DLFW/FogDrive/source/mcus/atmega328p.h

/*
    FogDrive (https://github.com/FogDrive/FogDrive)
    Copyright (C) 2016  Daniel Llin Ferrero

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
    You should have received a copy of the GNU General Public License
    along with this program.  If not, see <http://www.gnu.org/licenses/>.
*/

#ifndef ATMEGA328P_H
#define ATMEGA328P_H

#include <avr/io.h>

/**************************************************
 * UI input
 *************************************************/
#define HWMAP_UI_SWITCH_DDR      DDRB
#define HWMAP_UI_SWITCH_PORT     PORTB
#define HWMAP_UI_SWITCH_PIN      PINB
#define HWMAP_UI_SWITCH_0_IX     3

/**************************************************
 * UI output
 *************************************************/
#define HWMAP_UI_OUTPIN_DDR     DDRB
#define HWMAP_UI_OUTPIN_PORT    PORTB
#define HWMAP_UI_OUTPIN_0_IX    2

/**************************************************
 * UI timer for event timing
 *************************************************/
#define HWMAP_UI_TIMER_ISR     TIMER2_OVF_vect
#define HWMAP_UI_TIMER_CMD_REINIT_FOR_10ms TCNT2 = (256-(F_CPU / 256 * 10e-3 + 0.5));
// Function that initializes the UI timers and PWMs
void ui_timer_init_10ms_overflow(void);

/**************************************************
 * UI timer for LED PWM
 *************************************************/
#define MCU_UI_PWM_A_CR OCR0A
void mcu_init_ui_double_compare_timer_for_fast_pwm_1ms(void);

/**************************************************
 * UART
 *************************************************/
#define UART_ENABLED
// Baud rate for the UART, should be externalized somehow later on
#define BAUD 4800UL
// The UART's char buffer register (delivers in received character inside the ISR and takes a charater to write out)
#define CTRLMAP_UART_CHARBUFFER     UDR0
// Command that waits until the charbuffer is empty and can be used to send a single character
#define MCUMAP_UART_CMD_AWAIT_EMPTY_CHARBUFFER  while ( !( UCSR0A & (1<<UDRE0)) );
// Function that inititializes the UART with 8 data and one stop bit.
void uart_init_8_plus_1(void);

/**************************************************
 * Hardware fire pin
 *************************************************/
// Data register used to control the fire MOSFET
#define HWMAP_HW_FIRE_DDR        DDRB
// Corresponding port
#define HWMAP_HW_FIRE_PORT       PORTB
// Index of the pin used to control the fire MOSFET
#define HWMAP_HW_FIRE_BIT_IX     0

/**************************************************
 * Hardware ADC
 *************************************************/
void mcu__enabled_one_adc_with_vcc_reference_and_vgb_input(void);
#define MCU__START_SINGLE_ADC_CONVERSION ADCSRA |= (1<<ADSC)
#define MCU__SINGLE_ADC_CONVERSION_IS_DONE ! (ADCSRA & (1<<ADSC))

/**************************************************
 * Power Down
 *************************************************/
void mcu_power_down_till_pin_change(void);

#endif // ATMEGA328P_H
