DLFW/FogDrive/source/mcus/atmega328p.c

/*
    FogDrive (https://github.com/FogDrive/FogDrive)
    Copyright (C) 2016  Daniel Llin Ferrero

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
    You should have received a copy of the GNU General Public License
    along with this program.  If not, see <http://www.gnu.org/licenses/>.
*/

#include "atmega328p.h"
#include <avr/interrupt.h>
#include <avr/sleep.h>


// Baud rate related calculation
#define UBRR_VAL ((F_CPU+BAUD*8)/(BAUD*16)-1)   // clever runden
#define BAUD_REAL (F_CPU/(16*(UBRR_VAL+1)))     // Reale Baudrate
#define BAUD_ERROR ((BAUD_REAL*1000)/BAUD)      // Fehler in Promille, 1000 = kein Fehler.

#if ((BAUD_ERROR<990) || (BAUD_ERROR>1010))
#error Systematic error of baud rate to high (> 1%). Aborting.
#endif

void uart_init_8_plus_1(void) {
    UBRR0H = UBRR_VAL >> 8;
    UBRR0L = UBRR_VAL & 0xFF;
    UCSR0B |= (1<<TXEN0) | (1<<RXEN0) | (1<<RXCIE0);  // enable send, enable receive, enable receive interrupt
    UCSR0C = (1<<UCSZ01)| (1<<UCSZ00)|(1<<UCPOL0);    // asynch 8 bit + 1 stop bit
}

void ui_timer_init_10ms_overflow(void) {
    TCCR2B = (1<<CS22)|(1<<CS21);  // prescaler 256
    TIMSK2 = (1<<TOIE2);
    HWMAP_UI_TIMER_CMD_REINIT_FOR_10ms;
}

void mcu_init_ui_double_compare_timer_for_fast_pwm_1ms(void) {
    //TODO: it's only 1ms with 1MHz frequency: refactor name or function
    DDRD |= (1<<6);                                   // Set the pin of PWM channel A as output
    TCCR0A = (1<<WGM01) | (1<<WGM00) | (1<<COM0A1) | (1<<COM0A0);   // Fast PWM, single slope, count from 0 to 255 (not only till compare), inverting
    TCCR0B = (1<<CS00);                               // Internal clock, no prescaling
}

void mcu__enabled_one_adc_with_vcc_reference_and_vgb_input(void) {
    ADMUX |= (1<<REFS0);                         //voltage reference selction: AV_CC
    ADMUX |= (1<<MUX3) | (1<<MUX2) | (1<<MUX1);  //input voltage selection: 1.1V (V_BG)
    ADCSRA |= (1<<ADEN);                         //activate ADC
}

void mcu_power_down_till_pin_change(void) {
    PCICR |= (1 << PCIE0);                      //enable pin change iterrupt on PCINT[7..0] which includes the button
    PCMSK0 |= (1 << PCINT3);                    // and activate the PCINT for the button pin
    set_sleep_mode(SLEEP_MODE_PWR_DOWN);        // set sleep mode (power down, deepest sleep)...
    sleep_mode();                               // ...and enter it
    PCICR &= ~(1 << PCIE0);                     // we're waking up! disable pin change iterrupt on PCINT[7..0]
}

ISR(PCINT0_vect) {
    // Nothing to do in this interrupt routine.
    // It must just be defined since we need that interrupt to awake from "power down" sleep mode.
}
