DLFW/FogDrive/source/mira/deviface.c

/*
    FogDrive (https://github.com/FogDrive/FogDrive)
    Copyright (C) 2016  Daniel Llin Ferrero

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
    You should have received a copy of the GNU General Public License
    along with this program.  If not, see <http://www.gnu.org/licenses/>.
*/

#include <avr/io.h>
#include <avr/interrupt.h>
#include <string.h>
#include "queue.h"
#include "deviface.h"
#include MCUHEADER

volatile uint8_t uart_str_complete = 0;
volatile uint8_t uart_str_count = 0;
volatile char uart_string[UART_MAXSTRLEN + 1] = "";


#ifdef UART_ENABLED

void deviface_init(void) {
    uart_init_8_plus_1();
}

void deviface_putchar( unsigned char data ) {
#ifdef UART_ENABLED
    // Wait for empty transmit buffer (mcu specific macro)
    MCUMAP_UART_CMD_AWAIT_EMPTY_CHARBUFFER;
    // Put data into buffer (mcu specific macro), sends the data
    CTRLMAP_UART_CHARBUFFER = data;
#endif
}

void deviface_putstring (char* s) {
    while (*s) {
        deviface_putchar(*s);
        s++;
    }
}

void deviface_putlineend(void) {
    deviface_putstring("\r\n");
}

void deviface_putline (char* s) {
    deviface_putstring(s);
    deviface_putlineend();
}

void deviface_put_uint8(uint8_t v) {
    char value_s[4];
    utoa(v,value_s,10);
    deviface_putstring(value_s);
}

void deviface_put_int8(int8_t v) {
    char value_s[4];
    itoa(v,value_s,10);
    deviface_putstring(value_s);
}

void deviface_put_uint16(uint16_t v) {
    char value_s[6];
    utoa(v,value_s,10);
    deviface_putstring(value_s);
}

void deviface_put_float(float v, int8_t width, uint8_t prec) {
    char value_s[20];
    dtostrf(v, width, prec,value_s);
    deviface_putstring(value_s);
}

ISR(USART_RX_vect) {
#ifdef UART_ENABLED
  unsigned char nextChar;
  nextChar = CTRLMAP_UART_CHARBUFFER;
  if( uart_str_complete == 0 ) {
    if( nextChar != '\n' &&
        nextChar != '\r' &&
        uart_str_count < UART_MAXSTRLEN
    ) {
        uart_string[uart_str_count] = nextChar;
        uart_str_count++;
        deviface_putchar(nextChar);            // echo the character
    } else {
        uart_string[uart_str_count] = '\0';
        uart_str_count = 0;
        uart_str_complete = 1;
        deviface_putchar('\r');
        deviface_putchar('\n');
    }
  }
#endif
}

#endif
