DLFW/FogDrive/source/mira/ui.c

/*
    FogDrive (https://github.com/FogDrive/FogDrive)
    Copyright (C) 2016  Daniel Llin Ferrero

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
    You should have received a copy of the GNU General Public License
    along with this program.  If not, see <http://www.gnu.org/licenses/>.
*/

#include <avr/io.h>
#include <avr/interrupt.h>
#include <avr/delay.h>
#include "ui.h"
#include "logic.h"
#include "led.h"
#include "button.h"
#include MCUHEADER
#ifdef UART_ENABLED
    #include "deviface.h"
#endif

// Bit mask for switch 0
#define CTRLMAP_SWITCH_0_MASK   (1<<HWMAP_UI_SWITCH_0_IX)
// Bit mask for all used switches
#define ALL_SWITCHES            (1<<HWMAP_UI_SWITCH_0_IX)

// Bit mask for out pin 0 (LED)
#define OUTPIN_0_MASK           (1<<HWMAP_UI_OUTPIN_0_IX)
// Bit mask for all used out pins
#define OUTPIN_ALL_MASK         (1<<HWMAP_UI_OUTPIN_0_IX)

// Low Level Event codes (for the low_level_event_queue)
#define LLE_SWITCH_PRESSED 1    // a switch was pressed, switch index in 2nd queue element
#define LLE_SWITCH_RELEASED 2   // a switch was released, switch index in 2nd queue element
#define LLE_50MS_PULSE 3        // 50 ms pulse, this event is put in the queue each 50 ms

// User interface input queue (which is an external, see @ui.h#Queue ui_input_queue) and its element array
Queue ui_event_queue;
QueueElement ui_event_queue_elements[4];

/**
 * Queue that transports low level control events to the ui state machines.
 * It's used locally in this module only.
 * Its elements carry a "Low Level Event" (LLE_*) in byte a. In case the event refers to a switch,
 * the switch index is in byte b.
 */
static Queue low_level_event_queue;
/**
 * Queue array for #ui_input_queue.
 */
static QueueElement low_level_event_queue_array[3];

static LED led;

static Button button;

static uint8_t ui_local_bools = 0;
#define LB_PRINT_LED_INFO       1
#define LB_FIRE_IS_ON           2
#define LB_LOW_VOLTAGE_DETECTED 4
#define LB_VERY_LOW_VOLTAGE_DETECTED 8
#define LB_SWITCH_OFF_FORCED    16

/**
 * @brief Blends the LED from a value "from" to a value "to".
 */
void led_blend(void) {
    led_program_reset(&led);
    led_program_add_brightness(&led, 0);
    led_program_add_linear_dim(&led, 99, 50);
    led_program_add_brightness(&led, 0);
    led_start_program(&led);
}

uint8_t ui_init(void) {
    // init queues
    queue_initialize(&ui_event_queue, 4, ui_event_queue_elements);
    queue_initialize(&low_level_event_queue, 3, low_level_event_queue_array);

    // init switch pins
    HWMAP_UI_SWITCH_DDR &= ~ALL_SWITCHES;                // configure all input pins as input by setting the related direction bits to 0
    HWMAP_UI_SWITCH_PORT |= ALL_SWITCHES;                // turn on the pull up resistors of all input pins

    // init output pin
    HWMAP_UI_OUTPIN_DDR |= OUTPIN_ALL_MASK;             // configure output pins as output in the related data direction register
    HWMAP_UI_OUTPIN_PORT &= ~OUTPIN_ALL_MASK;           // initialize all output pins (set them off)

    // init the ui timer
    ui_timer_init_10ms_overflow();

    // init LED PWM
    mcu_init_ui_double_compare_timer_for_fast_pwm_1ms();
    led_init_led(&led, &MCU_UI_PWM_A_CR);

    // init button logic
    button_init(&button);

    led_blend();

    return 0;
}

/**
  * ISR for timer zero.
  * Configured to be called every 10ms.
  */
ISR( HWMAP_UI_TIMER_ISR ) {
    // initialize the timer again to get the wanted trigger frequency for this ISR
    HWMAP_UI_TIMER_CMD_REINIT_FOR_10ms;

    // debouncing counter bytes
    static uint8_t ct0 = 0xFF, ct1 = 0xFF;
    // latest debounced switch state (each bit represents one switch (bit) from the input register (PIN))
    static uint8_t switch_states = 0;
    // latest changed status (1 = changed, 0 = unchanged, each bit represents one switch (bit) from the input register (PIN))
    static uint8_t changed_switches = 0;
    // counter that just counts to five times and is resetted then to identify each 5th cycle of the 10ms branch
    static uint8_t _50ms_counter = 0;
    // stores the difference of the main cycle counter between each call and the former of this ISR
    static uint8_t last_main_cycle_counter = 0;

    // here we go...
    // debouncing:
    // basic debouncing strategy based on http://www.mikrocontroller.net/articles/Entprellung#Timer-Verfahren_.28nach_Peter_Dannegger.29
    //
    // set those bits in i to 1 which represents a switch whose actual state is different from the latest unbounced state (key_state)
    uint8_t i = switch_states ^ ~HWMAP_UI_SWITCH_PIN;
    // ct0 and ct1 bytes: count the number of subsequent differences between actual and last debounced state or set back it back to 0 if it's equal.
    ct0 = ~( ct0 & i );
    ct1 = ct0 ^ (ct1 & i);
    // for each switch that had 4 times an actual state different from the last debounced state, set the corresponding bit in i to 1
    i &= ct0 & ct1;
    // set the most current _debounced_ state of all switches
    switch_states ^= i;
    // create a bitmask of all _relevant_ switches that have changed
    changed_switches = i & ALL_SWITCHES;

    // check for concrete switch changes:
    // check for switch 0
    if (CTRLMAP_SWITCH_0_MASK & changed_switches) {
        QueueElement* e = queue_get_write_element(&low_level_event_queue);
        if (CTRLMAP_SWITCH_0_MASK & switch_states) {
            e->bytes.a = LLE_SWITCH_PRESSED;
        } else {
            e->bytes.a = LLE_SWITCH_RELEASED;
        }
        e->bytes.b = HWMAP_UI_SWITCH_0_IX;
    }

    if (++_50ms_counter == 5) {
        _50ms_counter = 0;
        QueueElement* e = queue_get_write_element(&low_level_event_queue);
        e->bytes.a = LLE_50MS_PULSE;
    }

    led_step(&led);
}

void _print_led_commands(LED* led) {
#ifdef UART_ENABLED
    uint8_t n = 0;
    for (n = 0; n < _LED_MAX_COMMAND_COUNT; n++) {
        deviface_putstring("  ");
        deviface_put_uint8(led->_commands[n].cmd);
        deviface_putstring(" ");
        deviface_put_uint8(led->_commands[n].generic.a);
        deviface_putstring(" ");
        deviface_put_uint8(led->_commands[n].generic.b);
        deviface_putstring(" ");
        deviface_put_uint8(led->_commands[n].generic.c);
        deviface_putlineend();
    }
#endif
}

void _callback_for_shutdown(LED *led) {
    // we are switched on (awake) and switch off now (go to sleep)
    QueueElement* e = queue_get_write_element(&ui_event_queue);
    e->bytes.a = UI__SWITCH_OFF;
}

void ui_input_step(void) {

    // Check for events from the timer ISR and react
    QueueElement* low_level_event_e = queue_get_read_element(&low_level_event_queue);
    if (low_level_event_e != 0) {
        if (low_level_event_e->bytes.a == LLE_SWITCH_PRESSED) {
            button_pressed(&button);
        }
        else if (low_level_event_e->bytes.a == LLE_SWITCH_RELEASED) {
            button_released(&button);
        }
        else if (low_level_event_e->bytes.a == LLE_50MS_PULSE) {
            QueueElement* e = queue_get_write_element(&ui_event_queue);
            e->bytes.a = UI__50MS_PULSE;
            button_step(&button);
        }
    }

    // Check for events from the button and react
    if (global_state == GS_AWAKENING) {
        QueueElement* button_event = queue_get_read_element(&(button.button_event_queue));
        if (button_event != 0) {
            if (button_event->bytes.a == BUTTON_EVENT_CLICK & button_event->bytes.b == 3) {
                QueueElement* e = queue_get_write_element(&ui_event_queue);
                e->bytes.a = UI__SWITCH_ON;
            } else {
                QueueElement* e = queue_get_write_element(&ui_event_queue);
                e->bytes.a = UI__ABORT_AWAKENING;
            }
        }

    } else {
        QueueElement* button_event = queue_get_read_element(&(button.button_event_queue));
        if (button_event != 0) {
            switch (button_event->bytes.a) {
                case BUTTON_EVENT_PRESSED: {
                    // button pressed: fire!
                    QueueElement* e = queue_get_write_element(&ui_event_queue);
                    e->bytes.a = UI__FIRE_BUTTON_PRESSED;
                    break;
                }
                case BUTTON_EVENT_RELEASED_TIMEOUT: {
                    led_blend();
                    break;
                }
                case BUTTON_EVENT_TIMEOUT:
                case BUTTON_EVENT_RELEASED: {
                    //button released: fire off!
                    QueueElement* e = queue_get_write_element(&ui_event_queue);
                    e->bytes.a = UI__FIRE_BUTTON_RELEASED;
                    break;
                }
                case BUTTON_EVENT_CLICK: {
                    // click sequence detected
                    switch (button_event->bytes.b) {
                        case 1:
                        {
                            led_blend();
                            break;
                        }

                        case 2:
                        {
                            if (battery_voltage_under_load > 0) {
                                // double click detected: "blink" the battery voltage under load
                                uint8_t digit1 = battery_voltage_under_load / 10;
                                uint8_t digit2 = battery_voltage_under_load - digit1*10;
                                led_set_brightness(&led, 0);
                                led_program_reset(&led);
                                led_program_add_linear_dim(&led, 99, 3);
                                led_program_add_hold(&led, 13);
                                led_program_add_linear_dim(&led, 0, 3);
                                led_program_add_hold(&led, 20);
                                led_program_repeat(&led, 0, digit1 - 1);
                                led_program_add_hold(&led,45);
                                if (digit2 > 0) {
                                    led_program_add_linear_dim(&led, 99, 3);
                                    led_program_add_hold(&led, 13);
                                    led_program_add_linear_dim(&led, 0, 3);
                                    led_program_add_hold(&led, 20);
                                    if (digit2 > 1) {
                                        led_program_repeat(&led, 6, digit2 - 1);
                                    }
                                }
                                led_start_program(&led);
                            }
                            break;
                        }
                        case 3:
                        {
                            led_program_reset(&led);
                            led_program_add_brightness(&led, 99);
                            led_program_add_linear_dim(&led, 0, 50);
                            led_program_add_brightness(&led, 0);
                            led_program_callback(&led, _callback_for_shutdown);
                            led_start_program(&led);
                        }
                    }
                    break;
                }
            }
        }

        // Check for pending tasks from the logic
        #ifdef UART_ENABLED
        if (ui_local_bools & LB_PRINT_LED_INFO) {
            ui_local_bools &= ~LB_PRINT_LED_INFO;
            deviface_putstring("LED 1# b: ");
            deviface_put_uint8(led._current_brightness);
            deviface_putstring(", ocr: ");
            deviface_put_uint8(MCU_UI_PWM_A_CR);
            deviface_putstring(", ccnt: ");
            deviface_put_uint8(led._command_count);
            deviface_putstring(", cix: ");
            deviface_put_uint8(led._current_command_ix);
            deviface_putlineend();
            _print_led_commands(&led);
        }
        #endif

        // Battery voltage indicator
        if (ui_local_bools & LB_FIRE_IS_ON) {
            if (battery_voltage_under_load > 0) {
                if (battery_voltage_under_load < BATTERY_VOLTAGE_LOW_VALUE) {
                    if (! (ui_local_bools & LB_LOW_VOLTAGE_DETECTED)) {
                        ui_local_bools |= LB_LOW_VOLTAGE_DETECTED;
                        led_program_reset(&led);
                        led_program_add_linear_dim(&led, 87, 20);
                        led_start_program(&led);
                    }
                }
                if (battery_voltage_under_load < BATTERY_VOLTAGE_VERY_LOW_VALUE) {
                    if (! (ui_local_bools & LB_VERY_LOW_VOLTAGE_DETECTED)) {
                        ui_local_bools |= LB_VERY_LOW_VOLTAGE_DETECTED;
                        led_program_reset(&led);
                        led_program_add_linear_dim(&led, 99, 10);
                        led_program_add_hold(&led,22);
                        led_program_add_linear_dim(&led, 0, 10);
                        led_program_add_hold(&led,8);
                        led_program_repeat(&led,0,0);
                        led_start_program(&led);
                    }
                }
            }
        }
    }
}

void ui_fire_is_on(void) {
    ui_local_bools |= LB_FIRE_IS_ON;
}

void ui_fire_is_off(void) {
    ui_local_bools &= ~LB_FIRE_IS_ON;
    ui_local_bools &= ~LB_LOW_VOLTAGE_DETECTED;
    ui_local_bools &= ~LB_VERY_LOW_VOLTAGE_DETECTED;
    led_set_brightness(&led, 0);
    if (ui_local_bools & LB_SWITCH_OFF_FORCED) {
        ui_local_bools &= ~ LB_SWITCH_OFF_FORCED;
        led_program_reset(&led);
        led_program_add_linear_dim(&led, 99, 10);
        led_program_add_linear_dim(&led, 0, 10);
        led_program_repeat(&led,0,0);
        led_start_program(&led);
    }
}

void ui_switch_off_forced(void) {
    ui_local_bools |= LB_SWITCH_OFF_FORCED;
}

void ui_print_led_info(void) {
    ui_local_bools |= LB_PRINT_LED_INFO;
}

void ui_power_down() {
    led_set_brightness(&led, 0);    // cancel any LED program if some is running and switch off the LED
    queue_clear(&ui_event_queue);   // remove unprocessed UI events if there are any
    _delay_ms(100);
    // the UI timer ISR is just freezed as it is
}

void ui_power_up() {
    led_blend();
}
